jamwaffles/optiplower/img/dell-65w-pcb-annotated.jpg

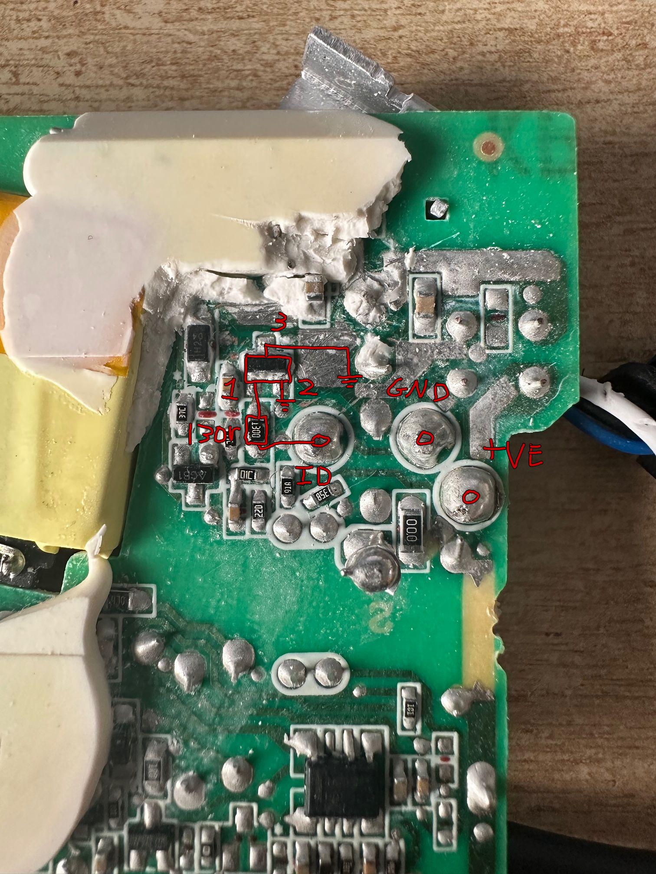
img/dell-65w-pcb-annotated.jpg
