jamwaffles/optiplower/img/dell-psu.png

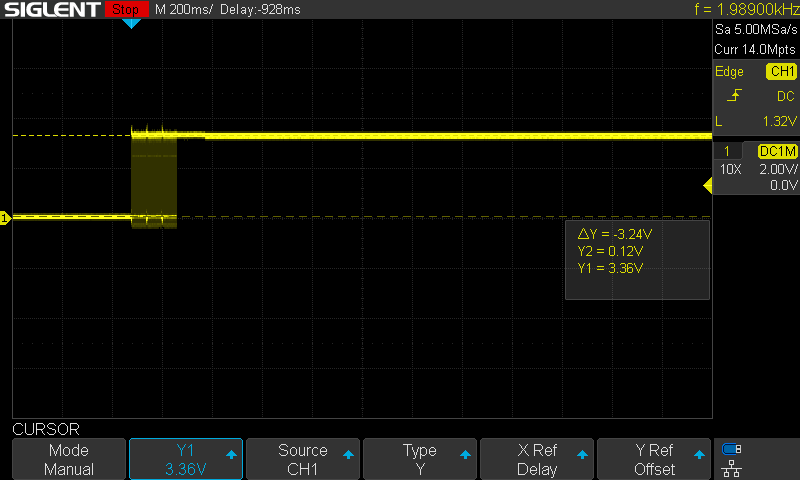
img/dell-psu.png
