jamwaffles/optiplower/img/pullups-3v3.png

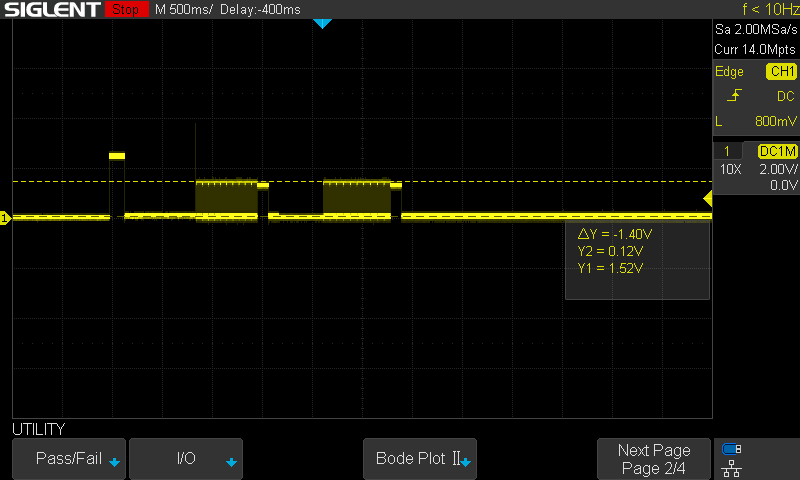
img/pullups-3v3.png
