jamwaffles/optiplower/img/pullups-disabled-2v7.png

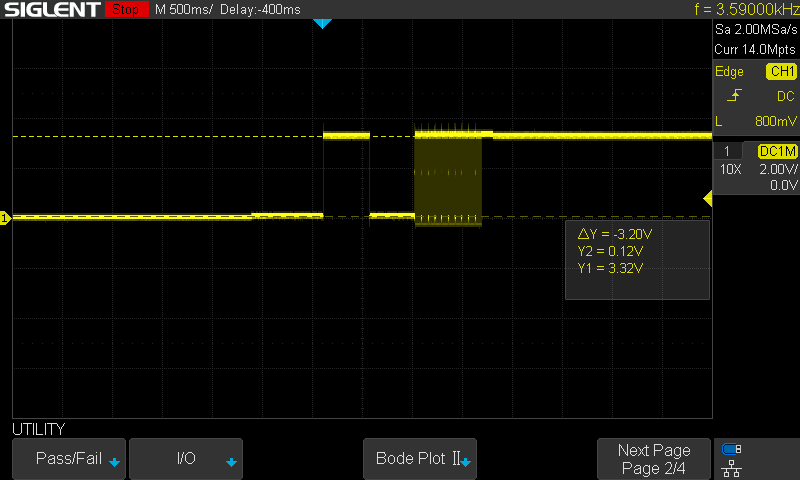
img/pullups-disabled-2v7.png
