jamwaffles/optiplower/img/pullups-disabled-3v3.png

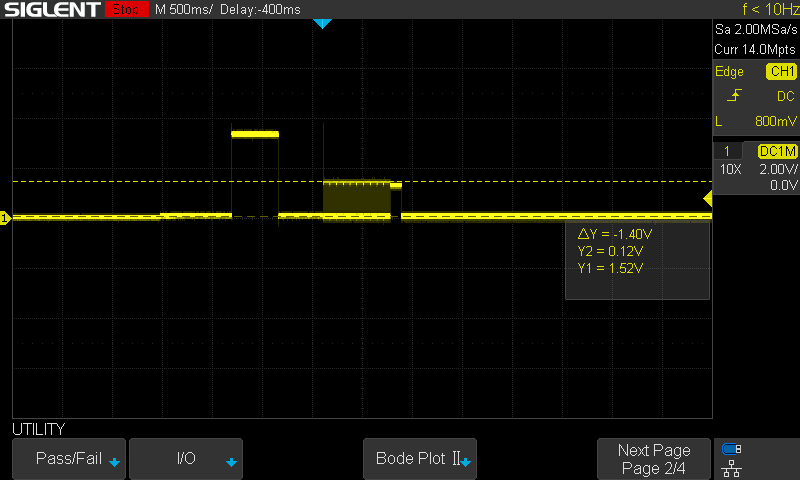
img/pullups-disabled-3v3.png
