jamwaffles/optiplower/ds2502-emulator/src/DS2502.h

// 1Kbit 1-Wire EEPROM, Add Only Memory
// works, writing could not be tested (DS9490 does not support hi-voltage mode and complains)
// native bus-features: none

#ifndef ONEWIRE_DS2502_H
#define ONEWIRE_DS2502_H

#include "OneWireItem.h"

// EEPROM strings, the length is always 42 bytes, including 2 bytes of CRC16/ARC checksum.
constexpr uint8_t chargerStrlen{42};

// 45W
// https://github.com/KivApple/dell-charger-emulator
// constexpr uint8_t char* memory = "DELL00AC045195023CN0CDF577243865Q27F2A05\x3D\x94";

// https://nickschicht.wordpress.com/2009/07/15/dell-power-supply-fault/
// 65W
constexpr const uint8_t *memory = "DELL00AC065195033CN05U0927161552F31B8A03\xBC\x8F";
// CRC checksup is correct for this string, but it seems it MUST include "DELL" at the beginning.
// constexpr const uint8_t *memory = "FOOF00AC065195033CN05U0927161552F31B8A03\xDE\x80";

// 90W
// constexpr uint8_t char* memory = "DELL00AC090195046CN0C80234866161R23H8A03\x4D\x7C";

// NOTE: XL4015 only supports about 90W! Never enable this option!
// 130W
// I made this up, works with Dell Inspiron 15R N5110 and Dell Inspiron 15R 5521
// constexpr uint8_t char* memory = "DELL00AC130195067CN0CDF577243865Q27F2233\x9D\x72";

class DS2502 : public OneWireItem
{
private:
    static constexpr uint8_t PAGE_COUNT{1};
    static constexpr uint8_t PAGE_SIZE{44}; // bytes
    static constexpr uint8_t PAGE_MASK{PAGE_SIZE - 1};

    static constexpr uint8_t MEM_SIZE{PAGE_COUNT * PAGE_SIZE}; // bytes
    static constexpr uint16_t MEM_MASK{MEM_SIZE - 1};

    static constexpr uint8_t STATUS_SIZE{8};

    static constexpr uint8_t STATUS_WP_PAGES{0x00}; // 1 byte -> Page write protection and page used status
    static constexpr uint8_t STATUS_PG_REDIR{0x01}; // 4 byte -> Page redirection
    static constexpr uint8_t STATUS_UNDEF_B1{0x05}; // 2 byte -> reserved / undefined
    static constexpr uint8_t STATUS_FACTORYP{0x07}; // 2 byte -> factoryprogrammed 0x00

    uint8_t status[STATUS_SIZE];                 // eprom status bytes:
    static constexpr uint8_t sizeof_memory{128}; // device specific "real" size

    uint8_t translateRedirection(uint8_t source_address) const;

public:
    static constexpr uint8_t family_code = 0x09; // the ds2502

    DS2502(uint8_t ID1, uint8_t ID2, uint8_t ID3, uint8_t ID4, uint8_t ID5, uint8_t ID6, uint8_t ID7);

    void duty(OneWireHub *hub) final;

    void clearMemory(void);
    void clearStatus(void);

    // bool writeMemory(const uint8_t *source, uint8_t length, uint8_t position = 0);
    // bool readMemory(uint8_t *destination, uint8_t length, uint8_t position = 0) const;

    uint8_t writeStatus(uint8_t address, uint8_t value);
    uint8_t readStatus(uint8_t address) const;

    void setPageProtection(uint8_t page);
    bool getPageProtection(uint8_t page) const;

    void setPageUsed(uint8_t page);
    bool getPageUsed(uint8_t page) const;

    bool setPageRedirection(uint8_t page_source, uint8_t page_destin);
    uint8_t getPageRedirection(uint8_t page) const;
};

#endif
